michaelmangelsdorf/myth/myth.kicad_sch

## KiCad design myth.kicad_sch (2025-06-29)

Schematic: myth.kicad_sch

Parts:
J1, J2, J4, J5, J6: Conn_01x08_Male; PinHeader_1x08_P2.54mm_Vertical
R1: A7.5k; R_Axial_DIN0207_L6.3mm_D2.5mm_P10.16mm_Horizontal
RN1, RN2: R_Network08 100K; R_Array_SIP9
U1, U40, U105, U213: 74AHC02; DIP-14_W7.62mm_Socket_LongPads
U2, U21, U31, U60, U64, U81, U93, U124, U142, U173, U174, U176, U177, U178, U179: 74AHC04; DIP-14_W7.62mm_Socket_LongPads
U3, U50, U63, U127, U132: 74HC74; DIP-14_W7.62mm_Socket_LongPads
U4, U13, U24, U211: 74LS11
U5, U17, U79, U84, U88, U92, U121, U191: 74AHC273; DIP-20_W7.62mm_Socket_LongPads
U6, U28: 74LS21
U7, U12, U18, U42, U87, U95, U114, U152, U158, U159, U168, U169, U170, U171, U172, U190, U194, U200, U201, U203, U205, U206, U210, U214, U216: 74AHC08; DIP-14_W7.62mm_Socket_LongPads
U8, U14, U15, U23: 74LS154
U9, U102, U106, U143, U218, U220: 74LS08; DIP-14_W7.62mm_Socket_LongPads
U10: 74HC595; DIP-16_W7.62mm_Socket_LongPads
U11: 74HC165; DIP-16_W7.62mm_Socket_LongPads
U16, U128: 74LS27
U19: CD4532BE; DIP-16_W7.62mm_Socket_LongPads
U20, U22, U34, U35, U47, U141: 74AHC138; DIP-16_W7.62mm_Socket_LongPads
U25, U38, U65, U101, U123, U138, U140, U160, U161, U162, U163, U164, U165, U166, U167, U186, U187, U195, U196, U197, U199, U204, U208, U209, U215: 74LS32; DIP-14_W7.62mm_Socket_LongPads
U26: 74AHC374
U27, U51, U61, U62, U82, U89, U91, U96, U97, U99, U136: 74AHC244; DIP-20_W7.62mm_Socket_LongPads
U30: 4075
U32, U36, U90, U103, U129: 74HC00; DIP-14_W7.62mm_Socket_LongPads
U33: 74HC163; DIP-16_W7.62mm_Socket_LongPads
U39: 74HC238; DIP-16_W7.62mm_Socket_LongPads
U41, U59, U78: 74AHC574; DIP-20_W7.62mm_Socket_LongPads
U43, U44, U48, U49, U73, U74, U85, U86, U111, U112, U113, U122, U175, U180: 74HC157; DIP-16_W7.62mm_Socket_LongPads
U45, U46, U53, U54, U55, U56, U69, U70, U80, U83: 74HC193; DIP-16_W7.62mm_Socket_LongPads
U52: 74HC02; DIP-14_W7.62mm_Socket_LongPads
U57, U144, U145, U198, U212, U217, U219: 4075; DIP-14_W7.62mm_Socket_LongPads
U58, U75, U135: 4078
U66, U67: 74LS257; DIP-16_W7.62mm_Socket_LongPads
U71, U72, U94, U181: 74HC283; DIP-16_W7.62mm_Socket_LongPads
U76: KM62256CLP; DIP-28_W15.24mm
U77: SST39SF040; DIP-32_W15.24mm_Socket_LongPads
U98, U150, U151, U153, U154, U155, U156, U157, U207: 4070
U104, U107, U108, U116: 74LS08
U109, U110, U117, U119, U120, U125, U126, U130, U131, U147, U148, U149, U182, U183, U185, U188, U192, U193: 74LS573; DIP-16_W7.62mm_Socket_LongPads
U115: 4002
U133, U134, U137, U146, U202: 4072
U139, U189, U222: 74HC85
U184: 4068
X1: CxO_DIP14; Oscillator_DIP-14

Connections:
+5V: J4.1, R1.1, U3.2 (D), U5.20 (VCC), U8.19 (E1), U8.24 (VCC), U10.16 (VCC), U11.16 (VCC), U14.19 (E1), U14.24 (VCC), U15.18 (E0), U15.19 (E1), U15.24 (VCC), U17.20 (VCC), U19.16 (VDD), U20.6 (E3), U20.16 (VCC), U22.16 (VCC), U23.18 (E0), U23.19 (E1), U23.24 (VCC), U26.20 (VCC), U27.20 (VCC), U33.7 (CEP), U33.9 (~PE), U33.10 (CET), U33.16 (VCC), U34.16 (VCC), U35.16 (VCC), U39.6 (G1), U39.16 (VCC), U41.20 (VCC), U43.16 (VCC), U44.16 (VCC), U45.11 (~LOAD), U45.16 (VCC), U46.11 (~LOAD), U46.16 (VCC), U47.6 (E3), U47.16 (VCC), U48.16 (VCC), U49.16 (VCC), U50.2 (D), U50.12 (D), U51.20 (VCC), U53.5 (UP), U53.16 (VCC), U54.16 (VCC), U55.4 (DOWN), U55.16 (VCC), U56.4 (DOWN), U56.16 (VCC), U58.14 (Vdd), U59.20 (VCC), U62.8 (1A3), U62.11 (2A3), U62.13 (2A2), U62.15 (2A1), U62.17 (2A0), U62.20 (VCC), U63.2 (D), U66.16 (VCC), U67.16 (VCC), U69.16 (VCC), U70.16 (VCC), U71.16 (VCC), U72.16 (VCC), U73.16 (VCC), U74.16 (VCC), U75.14 (Vdd), U76.28 (VCC), U77.31 (PGM), U77.32 (VCC), U78.20 (VCC), U79.20 (VCC), U80.16 (VCC), U82.20 (VCC), U83.16 (VCC), U84.20 (VCC), U85.16 (VCC), U86.16 (VCC), U88.20 (VCC), U89.20 (VCC), U91.20 (VCC), U92.20 (VCC), U94.16 (VCC), U96.20 (VCC), U97.20 (VCC), U99.20 (VCC), U109.20 (VCC), U110.20 (VCC), U111.16 (VCC), U112.16 (VCC), U113.16 (VCC), U117.20 (VCC), U119.20 (VCC), U120.20 (VCC), U121.20 (VCC), U122.6 (I1b), U122.16 (VCC), U125.20 (VCC), U126.20 (VCC), U127.2 (D), U130.20 (VCC), U131.20 (VCC), U132.2 (D), U135.14 (Vdd), U136.2 (1A0), U136.4 (1A1), U136.6 (1A2), U136.8 (1A3), U136.11 (2A3), U136.13 (2A2), U136.15 (2A1), U136.20 (VCC), U139.3 (Ia=b), U139.16 (VCC), U141.6 (E3), U141.16 (VCC), U147.20 (VCC), U148.20 (VCC), U149.20 (VCC), U175.16 (VCC), U180.16 (VCC), U181.16 (VCC), U182.20 (VCC), U183.20 (VCC), U184.14 (Vdd), U185.20 (VCC), U188.20 (VCC), U189.16 (VCC), U191.20 (VCC), U192.20 (VCC), U193.20 (VCC), U222.3 (Ia=b), U222.16 (VCC), X1.1 (EN), X1.14 (Vcc)
A0: U80.3 (QA), U91.2 (1A0), U124.9, U135.12, U139.10 (A0), U153.1, U159.12, U164.12, U175.2 (I0a), U191.3 (D0), U193.3 (D1), U201.13
A1: U80.2 (QB), U91.4 (1A1), U135.11, U139.12 (A1), U142.9, U151.1, U160.12, U168.12, U175.5 (I0b), U185.2 (D0), U191.4 (D1), U193.4 (D2)
A2: U80.6 (QC), U91.6 (1A2), U135.10, U139.13 (A2), U150.2, U165.13, U170.13, U173.9, U175.11 (I0c), U185.3 (D1), U191.7 (D2), U193.5 (D3)
A3: U80.7 (QD), U91.8 (1A3), U98.2, U135.9, U139.15 (A3), U161.13, U169.13, U174.9, U175.14 (I0d), U185.4 (D2), U191.8 (D3), U193.6 (D4)
A4: U83.3 (QA), U91.17 (2A0), U135.5, U156.2, U163.12, U171.13, U177.9, U180.2 (I0a), U185.5 (D3), U189.10 (A0), U191.13 (D4), U193.7 (D5)
A5: U83.2 (QB), U91.15 (2A1), U135.4, U157.2, U167.12, U172.13, U178.9, U180.5 (I0b), U185.6 (D4), U189.12 (A1), U191.14 (D5), U193.8 (D6)
A6: U83.6 (QC), U91.13 (2A2), U135.3, U152.12, U154.1, U162.13, U176.9, U180.11 (I0c), U185.7 (D5), U189.13 (A2), U191.17 (D6), U193.9 (D7)
A7: U42.9, U83.7 (QD), U91.11 (2A3), U135.2, U155.1, U158.12, U166.13, U179.9, U180.14 (I0d), U185.8 (D6), U189.15 (A3), U191.18 (D7), U200.12, U203.12, U207.2
ADDC: U194.13, U208.13
ADDV: U213.3, U216.12
AEX: U212.12
AGX: U212.13
ALX: U212.11
ASR: U203.13, U204.12
B0: U69.3 (QA), U78.2 (D0), U89.2 (1A0), U109.2 (D0), U117.2 (D0), U120.2 (D0), U125.2 (D0), U130.2 (D0)
B1: U69.2 (QB), U78.3 (D1), U89.4 (1A1), U109.3 (D1), U117.3 (D1), U120.3 (D1), U125.3 (D1), U130.3 (D1)
B2: U69.6 (QC), U78.4 (D2), U89.6 (1A2), U109.4 (D2), U117.4 (D2), U120.4 (D2), U125.4 (D2), U130.4 (D2)
B3: U69.7 (QD), U78.5 (D3), U89.8 (1A3), U109.5 (D3), U117.5 (D3), U120.5 (D3), U125.5 (D3), U130.5 (D3)
B4: U70.3 (QA), U78.6 (D4), U89.17 (2A0), U109.6 (D4), U117.6 (D4), U120.6 (D4), U125.6 (D4), U130.6 (D4)
B5: U70.2 (QB), U78.7 (D5), U89.15 (2A1), U109.7 (D5), U117.7 (D5), U120.7 (D5), U125.7 (D5), U130.7 (D5)
B6: U70.6 (QC), U78.8 (D6), U89.13 (2A2), U109.8 (D6), U117.8 (D6), U120.8 (D6), U125.8 (D6), U130.8 (D6)
B7: U70.7 (QD), U78.9 (D7), U89.11 (2A3), U109.9 (D7), U117.9 (D7), U120.9 (D7), U125.9 (D7), U130.9 (D7)
BOIA: U47.7 (O7), U187.12
BOP1: U47.14 (O1), U120.11 (Load), U126.11 (Load)
BOP2: U47.12 (O3), U125.11 (Load), U131.11 (Load)
BOP3: U47.10 (O5), U117.11 (Load), U119.11 (Load)
BUSY: J6.6, U132.5 (Q)
C0: U86.3 (I1a), U92.2 (Q0), U96.2 (1A0)
C1: U86.6 (I1b), U92.5 (Q1), U96.4 (1A1)
C2: U86.10 (I1c), U92.6 (Q2), U96.6 (1A2)
C3: U86.13 (I1d), U92.9 (Q3), U96.8 (1A3)
C4: U85.3 (I1a), U92.12 (Q4), U96.17 (2A0)
C5: U85.6 (I1b), U92.15 (Q5), U96.15 (2A1)
C6: U85.10 (I1c), U92.16 (Q6), U96.13 (2A2)
C7: U85.13 (I1d), U92.19 (Q7), U96.11 (2A3)
CAN_OVERFLOW: U210.13
CARRY: U173.1, U181.9 (C4), U194.12
CLEAR_A: U202.1
CLOCK: J2.1, U33.2 (CP)
CLOSE: J6.8, U1.6, U7.12, U12.12, U33.11 (Q3), U39.4 (~G2A), U40.2, U40.6, U42.12, U59.11 (Cp), U78.11 (Cp), U84.11 (Cp), U188.11 (Load), U191.11 (Cp)
CNEW0: U75.2, U88.2 (Q0), U92.3 (D0)
CNEW1: U75.3, U88.5 (Q1), U92.4 (D1)
CNEW2: U75.4, U88.6 (Q2), U92.7 (D2)
CNEW3: U75.5, U88.9 (Q3), U92.8 (D3)
CNEW4: U75.9, U88.12 (Q4), U92.13 (D4)
CNEW5: U75.10, U88.15 (Q5), U92.14 (D5)
CNEW6: U75.11, U88.16 (Q6), U92.17 (D6)
CNEW7: U75.12, U88.19 (Q7), U92.18 (D7)
CODE: U16.13, U123.13, U141.14 (O1), U219.12
COR: U28.5, U30.2
D0: U53.3 (QA), U58.2, U59.2 (D0)
D1: U53.2 (QB), U58.3, U59.3 (D1)
D2: U53.6 (QC), U58.4, U59.4 (D2)
D3: U53.7 (QD), U58.5, U59.5 (D3)
D4: U54.3 (QA), U58.9, U59.6 (D4)
D5: U54.2 (QB), U58.10, U59.7 (D5)
D6: U54.6 (QC), U58.11, U59.8 (D6)
D7: U54.7 (QD), U58.12, U59.9 (D7)
DB0: RN2.2 (R1), U10.15 (QA), U11.11 (D0), U17.3 (D0), U26.2 (O0), U27.18 (1Y0), U41.2 (D0), U43.3 (I1a), U45.15 (A), U53.15 (A), U59.19 (Q0), U71.6 (B1), U73.2 (I0a), U76.11 (Q0), U77.13 (D0), U80.15 (A), U82.18 (1Y0), U86.2 (I0a), U88.3 (D0), U89.18 (1Y0), U91.18 (1Y0), U97.18 (1Y0), U110.19 (Q0), U111.2 (I0a), U119.19 (Q0), U126.19 (Q0), U131.19 (Q0), U136.18 (1Y0), U147.19 (Q0), U148.19 (Q0), U149.19 (Q0), U182.19 (Q0), U183.19 (Q0), U185.19 (Q0), U188.19 (Q0), U192.19 (Q0), U193.19 (Q0)
DB1: RN2.3 (R2), U10.1 (QB), U11.12 (D1), U17.4 (D1), U26.5 (O1), U27.16 (1Y1), U41.3 (D1), U43.6 (I1b), U45.1 (B), U53.1 (B), U59.18 (Q1), U71.2 (B2), U73.5 (I0b), U76.12 (Q1), U77.14 (D1), U80.1 (B), U82.16 (1Y1), U86.5 (I0b), U88.4 (D1), U89.16 (1Y1), U91.16 (1Y1), U97.16 (1Y1), U110.18 (Q1), U111.5 (I0b), U119.18 (Q1), U126.18 (Q1), U131.18 (Q1), U136.16 (1Y1), U147.18 (Q1), U148.18 (Q1), U149.18 (Q1), U182.18 (Q1), U183.18 (Q1), U185.18 (Q1), U188.18 (Q1), U192.18 (Q1), U193.18 (Q1)
DB2: RN2.4 (R3), U10.2 (QC), U11.13 (D2), U17.7 (D2), U26.6 (O2), U27.14 (1Y2), U41.4 (D2), U43.10 (I1c), U45.10 (C), U53.10 (C), U59.17 (Q2), U71.15 (B3), U73.11 (I0c), U76.13 (Q2), U77.15 (D2), U80.10 (C), U82.14 (1Y2), U86.11 (I0c), U88.7 (D2), U89.14 (1Y2), U91.14 (1Y2), U97.14 (1Y2), U110.17 (Q2), U111.11 (I0c), U119.17 (Q2), U126.17 (Q2), U131.17 (Q2), U136.14 (1Y2), U147.17 (Q2), U148.17 (Q2), U149.17 (Q2), U182.17 (Q2), U183.17 (Q2), U185.17 (Q2), U188.17 (Q2), U192.17 (Q2), U193.17 (Q2)
DB3: RN2.5 (R4), U10.3 (QD), U11.14 (D3), U17.8 (D3), U26.9 (O3), U27.12 (1Y3), U41.5 (D3), U43.13 (I1d), U45.9 (D), U53.9 (D), U59.16 (Q3), U71.11 (B4), U73.14 (I0d), U76.15 (Q3), U77.17 (D3), U80.9 (D), U82.12 (1Y3), U86.14 (I0d), U88.8 (D3), U89.12 (1Y3), U91.12 (1Y3), U97.12 (1Y3), U110.16 (Q3), U111.14 (I0d), U119.16 (Q3), U126.16 (Q3), U131.16 (Q3), U136.12 (1Y3), U147.16 (Q3), U148.16 (Q3), U149.16 (Q3), U182.16 (Q3), U183.16 (Q3), U185.16 (Q3), U188.16 (Q3), U192.16 (Q3), U193.16 (Q3)
DB4: RN2.6 (R5), U10.4 (QE), U11.3 (D4), U17.13 (D4), U26.12 (O4), U27.3 (2Y0), U41.6 (D4), U44.3 (I1a), U46.15 (A), U54.15 (A), U59.15 (Q4), U72.6 (B1), U74.2 (I0a), U76.16 (Q4), U77.18 (D4), U82.3 (2Y0), U83.15 (A), U85.2 (I0a), U88.13 (D4), U89.3 (2Y0), U91.3 (2Y0), U97.3 (2Y0), U110.15 (Q4), U119.15 (Q4), U122.2 (I0a), U126.15 (Q4), U131.15 (Q4), U136.3 (2Y0), U147.15 (Q4), U148.15 (Q4), U149.15 (Q4), U182.15 (Q4), U183.15 (Q4), U185.15 (Q4), U188.15 (Q4), U192.15 (Q4), U193.15 (Q4)
DB5: RN2.7 (R6), U10.5 (QF), U11.4 (D5), U17.14 (D5), U26.15 (O5), U27.5 (2Y1), U41.7 (D5), U44.6 (I1b), U46.1 (B), U54.1 (B), U59.14 (Q5), U72.2 (B2), U74.5 (I0b), U76.17 (Q5), U77.19 (D5), U82.5 (2Y1), U83.1 (B), U85.5 (I0b), U88.14 (D5), U89.5 (2Y1), U91.5 (2Y1), U97.5 (2Y1), U110.14 (Q5), U119.14 (Q5), U122.5 (I0b), U126.14 (Q5), U131.14 (Q5), U136.5 (2Y1), U147.14 (Q5), U148.14 (Q5), U149.14 (Q5), U182.14 (Q5), U183.14 (Q5), U185.14 (Q5), U188.14 (Q5), U192.14 (Q5), U193.14 (Q5)
DB6: RN2.8 (R7), U10.6 (QG), U11.5 (D6), U17.17 (D6), U26.16 (O6), U27.7 (2Y2), U41.8 (D6), U44.10 (I1c), U46.10 (C), U54.10 (C), U59.13 (Q6), U72.15 (B3), U74.11 (I0c), U76.18 (Q6), U77.20 (D6), U82.7 (2Y2), U83.10 (C), U85.11 (I0c), U88.17 (D6), U89.7 (2Y2), U91.7 (2Y2), U97.7 (2Y2), U110.13 (Q6), U119.13 (Q6), U122.11 (I0c), U126.13 (Q6), U131.13 (Q6), U136.7 (2Y2), U147.13 (Q6), U148.13 (Q6), U149.13 (Q6), U182.13 (Q6), U183.13 (Q6), U185.13 (Q6), U188.13 (Q6), U192.13 (Q6), U193.13 (Q6)
DB7: RN2.9 (R8), U9.5, U10.7 (QH), U11.6 (D7), U17.18 (D7), U26.19 (O7), U27.9 (2Y3), U41.9 (D7), U44.13 (I1d), U46.9 (D), U54.9 (D), U59.12 (Q7), U72.11 (B4), U74.14 (I0d), U76.19 (Q7), U77.21 (D7), U82.9 (2Y3), U83.9 (D), U85.14 (I0d), U88.18 (D7), U89.9 (2Y3), U91.9 (2Y3), U93.1, U97.9 (2Y3), U110.12 (Q7), U119.12 (Q7), U122.14 (I0d), U126.12 (Q7), U131.12 (Q7), U136.9 (2Y3), U147.12 (Q7), U148.12 (Q7), U149.12 (Q7), U182.12 (Q7), U183.12 (Q7), U185.12 (Q7), U188.12 (Q7), U192.12 (Q7), U193.12 (Q7)
DEC: U141.9 (O6)
DID_OVERFLOW: U210.11, U216.13
DPH: U33.12 (Q2), U35.6 (E3), U39.3 (A2), U40.5
EA: U141.7 (O7)
EH0: U15.23 (A0), U17.12 (Q4), U97.17 (2A0)
EH1: U15.22 (A1), U17.15 (Q5), U97.15 (2A1)
EH2: U15.21 (A2), U17.16 (Q6), U97.13 (2A2)
EH3: U15.20 (A3), U17.19 (Q7), U97.11 (2A3)
EL0: U17.2 (Q0), U23.23 (A0), U97.2 (1A0)
EL1: U17.5 (Q1), U23.22 (A1), U97.4 (1A1)
EL2: U17.6 (Q2), U23.21 (A2), U97.6 (1A2)
EL3: U17.9 (Q3), U23.20 (A3), U97.8 (1A3)
ENTER: U141.11 (O4)
EXIT: U48.1 (S), U49.1 (S), U85.1 (S), U86.1 (S), U88.11 (Cp), U115.3, U123.12
FBIT0: U196.12, U199.11
FBIT7: U197.13, U201.11
FEQ: U189.6 (Oa=b), U198.13
FETCH: U66.1 (S), U67.1 (S)
FGT: U189.5 (Oa>b), U198.11
FLT: U189.7 (Oa<b), U198.12
Fx: U38.13
GET: U128.2
GETB: U115.4
GETD: U105.3
GETO: U57.12
GETPUT: U1.1, U32.1, U32.10, U34.6 (E3), U60.11, U61.1 (1OE), U61.19 (2OE)
GND: J6.5, RN1.1 (common), RN2.1 (common), U3.3 (C), U5.10 (GND), U8.12 (GND), U10.8 (GND), U11.8 (GND), U11.10 (DS), U11.15 (~CE), U14.12 (GND), U15.12 (GND), U17.10 (GND), U19.2 (D5), U19.3 (D6), U19.4 (D7), U19.8 (VSS), U20.5 (E2), U20.8 (GND), U22.4 (E1), U22.8 (GND), U23.12 (GND), U26.10 (GND), U27.10 (GND), U27.11 (2A3), U27.13 (2A2), U27.15 (2A1), U33.3 (D0), U33.4 (D1), U33.5 (D2), U33.6 (D3), U33.8 (GND), U34.4 (E1), U34.5 (E2), U34.8 (GND), U35.8 (GND), U39.5 (~G2B), U39.8 (GND), U41.10 (GND), U43.8 (GND), U43.15 (E), U44.8 (GND), U44.15 (E), U45.8 (GND), U46.8 (GND), U47.5 (E2), U47.8 (GND), U48.8 (GND), U48.15 (E), U49.8 (GND), U49.15 (E), U50.3 (C), U50.11 (C), U51.10 (GND), U53.8 (GND), U54.8 (GND), U55.8 (GND), U56.8 (GND), U58.7 (Vss), U59.10 (GND), U61.10 (GND), U62.10 (GND), U63.3 (C), U66.8 (GND), U66.15 (OE), U67.8 (GND), U67.15 (OE), U69.8 (GND), U70.8 (GND), U71.7 (C0), U71.8 (GND), U72.8 (GND), U73.8 (GND), U73.15 (E), U74.8 (GND), U74.15 (E), U75.7 (Vss), U76.14 (GND), U77.1 (A18), U77.2 (A16), U77.3 (A15), U77.16 (GND), U77.30 (A17), U78.10 (GND), U79.10 (GND), U80.8 (GND), U82.10 (GND), U83.8 (GND), U84.10 (GND), U85.8 (GND), U85.15 (E), U86.8 (GND), U86.15 (E), U88.10 (GND), U89.10 (GND), U91.10 (GND), U92.10 (GND), U94.8 (GND), U96.10 (GND), U97.10 (GND), U99.10 (GND), U109.10 (GND), U110.10 (GND), U111.3 (I1a), U111.6 (I1b), U111.8 (GND), U111.10 (I1c), U111.13 (I1d), U111.15 (E), U112.8 (GND), U112.15 (E), U113.8 (GND), U113.15 (E), U117.10 (GND), U119.10 (GND), U120.10 (GND), U121.10 (GND), U122.3 (I1a), U122.8 (GND), U122.10 (I1c), U122.13 (I1d), U122.15 (E), U125.10 (GND), U126.10 (GND), U127.3 (C), U130.10 (GND), U131.10 (GND), U132.3 (C), U135.7 (Vss), U136.10 (GND), U136.17 (2A0), U139.2 (Ia<b), U139.4 (Ia>b), U139.8 (GND), U141.4 (E1), U141.8 (GND), U147.10 (GND), U148.10 (GND), U149.10 (GND), U175.8 (GND), U175.15 (E), U180.8 (GND), U180.15 (E), U181.8 (GND), U182.10 (GND), U183.10 (GND), U184.7 (Vss), U185.10 (GND), U188.10 (GND), U189.8 (GND), U191.10 (GND), U192.10 (GND), U193.2 (D0), U193.10 (GND), U222.2 (Ia<b), U222.4 (Ia>b), U222.8 (GND), U222.15 (A3), X1.7 (GND)
HI0: U51.18 (1Y0), U76.25 (A8), U77.27 (A8), U78.19 (Q0), U96.18 (1Y0), U99.18 (1Y0), U112.3 (I1a), U130.19 (Q0)
HI1: U51.16 (1Y1), U76.24 (A9), U77.26 (A9), U78.18 (Q1), U96.16 (1Y1), U99.16 (1Y1), U112.6 (I1b), U130.18 (Q1)
HI2: U51.14 (1Y2), U76.21 (A10), U77.23 (A10), U78.17 (Q2), U96.14 (1Y2), U99.14 (1Y2), U112.10 (I1c), U130.17 (Q2)
HI3: U51.12 (1Y3), U76.23 (A11), U77.25 (A11), U78.16 (Q3), U96.12 (1Y3), U99.12 (1Y3), U112.13 (I1d), U130.16 (Q3)
HI4: U51.3 (2Y0), U76.2 (A12), U77.4 (A12), U78.15 (Q4), U96.3 (2Y0), U99.3 (2Y0), U113.3 (I1a), U130.15 (Q4)
HI5: U51.5 (2Y1), U76.26 (A13), U77.28 (A13), U78.14 (Q5), U96.5 (2Y1), U99.5 (2Y1), U113.6 (I1b), U130.14 (Q5)
HI6: U51.7 (2Y2), U76.1 (A14), U77.29 (A14), U78.13 (Q6), U96.7 (2Y2), U99.7 (2Y2), U113.10 (I1c), U130.13 (Q6)
HI7: U51.9 (2Y3), U64.1, U77.22 (CE), U78.12 (Q7), U96.9 (2Y3), U99.9 (2Y3), U113.13 (I1d), U130.12 (Q7)
IABO: U47.9 (O6), U138.12
IA_LE: U109.11 (Load), U110.11 (Load), U187.11
IB0: RN1.2 (R1), RN1.9 (R8), U5.2 (Q0), U5.19 (Q7), U8.23 (A0), U14.23 (A0), U19.1 (D4), U20.1 (A0), U26.3 (D0), U26.18 (D7), U27.2 (1A0), U41.12 (Q7), U41.19 (Q0), U47.1 (A0), U62.2 (1A0), U141.1 (A0), U142.1, U222.9 (B0)
IB0_pre: U5.3 (D0), U111.4 (Za)
IB1: RN1.3 (R2), RN1.8 (R7), U5.5 (Q1), U5.16 (Q6), U8.22 (A1), U14.22 (A1), U19.13 (D3), U20.2 (A1), U26.4 (D1), U26.17 (D6), U27.4 (1A1), U35.3 (A2), U41.13 (Q6), U41.18 (Q1), U47.2 (A1), U62.4 (1A1), U141.2 (A1), U145.11, U146.4, U222.11 (B1), U222.13 (A2)
IB1_pre: U5.4 (D1), U111.7 (Zb)
IB2: RN1.4 (R3), RN1.7 (R6), U5.6 (Q2), U5.15 (Q5), U8.21 (A2), U14.21 (A2), U19.12 (D2), U20.3 (A2), U26.7 (D2), U26.14 (D5), U27.6 (1A2), U34.2 (A1), U35.2 (A1), U41.14 (Q5), U41.17 (Q2), U47.3 (A2), U62.6 (1A2), U141.3 (A2), U145.12, U146.3, U222.12 (A1), U222.14 (B2)
IB2_pre: U5.7 (D2), U111.9 (Zc)
IB3: RN1.5 (R4), RN1.6 (R5), U5.9 (Q3), U5.12 (Q4), U8.20 (A3), U14.20 (A3), U19.10 (D0), U19.11 (D1), U26.8 (D3), U26.13 (D4), U27.8 (1A3), U27.17 (2A0), U31.1, U32.9, U34.1 (A0), U34.3 (A2), U35.1 (A0), U41.15 (Q4), U41.16 (Q3), U145.13, U146.2, U222.1 (B3), U222.10 (A0)
IB3_pre: U5.8 (D3), U111.12 (Zd)
IB4_pre: U5.13 (D4), U122.4 (Za)
IB5_pre: U5.14 (D5), U122.7 (Zb)
IB6_pre: U5.17 (D6), U122.9 (Zc)
IB7_pre: U5.18 (D7), U122.12 (Zd)
INC: U141.10 (O5)
IPH: U16.2, U40.4, U128.1
JUMP: U36.4, U43.1 (S), U44.1 (S), U137.1
KEY: U65.5, U130.11 (Load), U217.10
L0: U45.3 (QA), U51.2 (1A0), U99.2 (1A0)
L1: U45.2 (QB), U51.4 (1A1), U99.4 (1A1)
L2: U45.6 (QC), U51.6 (1A2), U99.6 (1A2)
L3: U45.7 (QD), U51.8 (1A3), U99.8 (1A3)
L4: U46.3 (QA), U51.17 (2A0), U99.17 (2A0)
L5: U46.2 (QB), U51.15 (2A1), U99.15 (2A1)
L6: U46.6 (QC), U51.13 (2A2), U99.13 (2A2)
L7: U46.7 (QD), U51.11 (2A3), U99.11 (2A3)
LATCH_POINTER: U133.1, U134.2, U219.11
LEAVE: U141.12 (O3)
LFETCH: U16.1, U40.3, U143.11
LL0: U61.18 (1Y0), U62.18 (1Y0), U66.2 (I0a)
LL1: U61.16 (1Y1), U62.16 (1Y1), U66.5 (I0b)
LL2: U61.14 (1Y2), U62.14 (1Y2), U66.14 (I0c)
LL3: U61.12 (1Y3), U62.12 (1Y3), U66.11 (I0d)
LL4: U61.3 (2Y0), U62.3 (2Y0), U67.2 (I0a)
LL5: U61.5 (2Y1), U62.5 (2Y1), U67.5 (I0b)
LL6: U61.7 (2Y2), U62.7 (2Y2), U67.14 (I0c)
LL7: U61.9 (2Y3), U62.9 (2Y3), U67.11 (I0d)
LO0: U66.4 (Za), U76.10 (A0), U77.12 (A0)
LO1: U66.7 (Zb), U76.9 (A1), U77.11 (A1)
LO2: U66.12 (Zc), U76.8 (A2), U77.10 (A2)
LO3: U66.9 (Zd), U76.7 (A3), U77.9 (A3)
LO4: U67.4 (Za), U76.6 (A4), U77.8 (A4)
LO5: U67.7 (Zb), U76.5 (A5), U77.7 (A5)
LO6: U67.12 (Zc), U76.4 (A6), U77.6 (A6)
LO7: U67.9 (Zd), U76.3 (A7), U77.5 (A7)
LOCAL: U138.13, U141.13 (O2)
MISO: J6.3, R1.2, U2.11
MOSI: J6.2, U11.9 (Q7)
Mx: U38.12
Mx_pre: U52.5
NOTA0: U124.8, U175.3 (I1a), U192.2 (D0)
NOTA1: U142.8, U175.6 (I1b), U192.3 (D1)
NOTA2: U173.8, U175.10 (I1c), U192.4 (D2)
NOTA3: U174.8, U175.13 (I1d), U192.5 (D3)
NOTA4: U177.8, U180.3 (I1a), U192.6 (D4)
NOTA5: U178.8, U180.6 (I1b), U192.7 (D5)
NOTA6: U176.8, U180.10 (I1c), U192.8 (D6)
NOTA7: U179.8, U180.13 (I1d), U192.9 (D7)
NZFLAG_A: U7.4, U135.1
NZFLAG_D: U7.9, U58.1
unnamed: U1.4, U33.1 (~MR)
unnamed: U1.13, U3.1 (~R)
unnamed: U2.10, U2.13
unnamed: U4.2, U63.5 (Q)
unnamed: U9.6, U90.4
unnamed: U2.12, U10.14 (SER)
unnamed: U12.8, U38.4
unnamed: U12.11, U92.11 (Cp)
unnamed: U12.13, U50.5 (Q)
unnamed: U6.5, U13.12
unnamed: U14.18 (E0), U174.2
unnamed: U16.12, U96.1 (1OE), U96.19 (2OE)
unnamed: U19.6 (Q2), U22.3 (A2)
unnamed: U19.7 (Q1), U22.2 (A1)
unnamed: U19.9 (Q0), U22.1 (A0)
unnamed: U19.14 (GS), U22.6 (E3)
unnamed: U28.1, U36.6
unnamed: U30.9, U32.4
unnamed: U31.2, U32.2
unnamed: U33.13 (Q1), U39.2 (A1)
unnamed: U33.14 (Q0), U39.1 (A0)
unnamed: U38.5, U42.8
unnamed: U40.1, U55.5 (UP)
unnamed: U42.11, U53.4 (DOWN)
unnamed: U48.2 (I0a), U73.4 (Za)
unnamed: U48.4 (Za), U79.3 (D0)
unnamed: U48.5 (I0b), U73.7 (Zb)
unnamed: U48.7 (Zb), U79.4 (D1)
unnamed: U48.9 (Zc), U79.7 (D2)
unnamed: U48.11 (I0c), U73.9 (Zc)
unnamed: U48.12 (Zd), U79.8 (D3)
unnamed: U48.14 (I0d), U73.12 (Zd)
unnamed: U49.2 (I0a), U74.4 (Za)
unnamed: U49.4 (Za), U79.13 (D4)
unnamed: U49.5 (I0b), U74.7 (Zb)
unnamed: U49.7 (Zb), U79.14 (D5)
unnamed: U49.9 (Zc), U79.17 (D6)
unnamed: U49.11 (I0c), U74.9 (Zc)
unnamed: U49.12 (Zd), U79.18 (D7)
unnamed: U49.14 (I0d), U74.12 (Zd)
unnamed: U7.13, U50.9 (Q)
unnamed: U51.1 (1OE), U51.19 (2OE), U60.10, U62.1 (1OE), U62.19 (2OE)
unnamed: U52.4, U65.12
unnamed: U55.12 (~CO), U56.5 (UP)
unnamed: U55.14 (CLR), U56.14 (CLR), U65.3
unnamed: U7.11, U65.1
unnamed: U65.11, U78.1 (OE)
unnamed: U71.1 (S2), U73.6 (I1b)
unnamed: U71.4 (S1), U73.3 (I1a)
unnamed: U71.9 (C4), U72.7 (C0)
unnamed: U71.10 (S4), U73.13 (I1d)
unnamed: U71.13 (S3), U73.10 (I1c)
unnamed: U72.1 (S2), U74.6 (I1b)
unnamed: U72.4 (S1), U74.3 (I1a)
unnamed: U72.10 (S4), U74.13 (I1d)
unnamed: U72.13 (S3), U74.10 (I1c)
unnamed: U9.4, U81.2
unnamed: U91.1 (1OE), U91.19 (2OE), U95.11
unnamed: U101.11, U129.5
unnamed: U101.13, U102.11
unnamed: U72.9 (C4), U81.1, U102.4
unnamed: U93.2, U102.5
unnamed: U102.6, U103.4
unnamed: U104.11, U128.13
unnamed: U38.11, U104.13
unnamed: U53.11 (~LOAD), U54.11 (~LOAD), U105.1
unnamed: U45.4 (DOWN), U107.11
unnamed: U45.5 (UP), U108.11
unnamed: U4.12, U111.1 (S), U122.1 (S)
unnamed: U112.1 (S), U113.1 (S), U115.5, U219.10
unnamed: U86.4 (Za), U112.2 (I0a)
unnamed: U69.15 (A), U112.4 (Za)
unnamed: U86.7 (Zb), U112.5 (I0b)
unnamed: U69.1 (B), U112.7 (Zb)
unnamed: U69.10 (C), U112.9 (Zc)
unnamed: U86.9 (Zc), U112.11 (I0c)
unnamed: U69.9 (D), U112.12 (Zd)
unnamed: U86.12 (Zd), U112.14 (I0d)
unnamed: U85.4 (Za), U113.2 (I0a)
unnamed: U70.15 (A), U113.4 (Za)
unnamed: U85.7 (Zb), U113.5 (I0b)
unnamed: U70.1 (B), U113.7 (Zb)
unnamed: U70.10 (C), U113.9 (Zc)
unnamed: U85.9 (Zc), U113.11 (I0c)
unnamed: U70.9 (D), U113.12 (Zd)
unnamed: U85.12 (Zd), U113.14 (I0d)
unnamed: U59.1 (OE), U114.11
unnamed: U69.11 (~LOAD), U70.11 (~LOAD), U115.1
unnamed: U121.3 (D0), U196.11
unnamed: U121.4 (D1), U191.5 (Q1)
unnamed: U121.7 (D2), U191.6 (Q2)
unnamed: U121.8 (D3), U191.9 (Q3)
unnamed: U121.11 (Cp), U190.11
unnamed: U121.13 (D4), U191.12 (Q4)
unnamed: U121.14 (D5), U191.15 (Q5)
unnamed: U121.17 (D6), U191.16 (Q6)
unnamed: U121.18 (D7), U197.11
unnamed: U63.4 (~S), U123.3
unnamed: U57.11, U123.11
unnamed: U80.11 (~LOAD), U83.11 (~LOAD), U124.1, U209.11
unnamed: U124.2, U190.12
unnamed: U42.13, U127.5 (Q)
unnamed: U76.27 (~WE), U129.6
unnamed: U4.13, U132.6 (~Q)
unnamed: U133.5, U138.11
unnamed: U79.11 (Cp), U134.1
unnamed: U57.10, U134.5
unnamed: U7.8, U137.2
unnamed: U7.6, U137.4
unnamed: U38.6, U137.5
unnamed: U139.5 (Oa>b), U189.4 (Ia>b)
unnamed: U139.6 (Oa=b), U189.3 (Ia=b)
unnamed: U139.7 (Oa<b), U189.2 (Ia<b)
unnamed: U89.1 (1OE), U89.19 (2OE), U140.11
unnamed: U24.12, U140.13
unnamed: U141.15 (O0), U218.12
unnamed: U142.2, U146.5
unnamed: U147.2 (D0), U164.11
unnamed: U147.3 (D1), U160.11
unnamed: U147.4 (D2), U165.11
unnamed: U147.5 (D3), U161.11
unnamed: U147.6 (D4), U163.11
unnamed: U147.7 (D5), U167.11
unnamed: U147.8 (D6), U162.11
unnamed: U147.9 (D7), U166.11
unnamed: U148.2 (D0), U159.11
unnamed: U148.3 (D1), U168.11
unnamed: U148.4 (D2), U170.11
unnamed: U148.5 (D3), U169.11
unnamed: U148.6 (D4), U171.11
unnamed: U148.7 (D5), U172.11
unnamed: U148.8 (D6), U152.11
unnamed: U148.9 (D7), U158.11
unnamed: U149.2 (D0), U153.3
unnamed: U149.3 (D1), U151.3
unnamed: U149.4 (D2), U150.3
unnamed: U98.3, U149.5 (D3)
unnamed: U149.6 (D4), U156.3
unnamed: U149.7 (D5), U157.3
unnamed: U149.8 (D6), U154.3
unnamed: U173.2, U206.12
unnamed: U94.5 (A1), U175.4 (Za)
unnamed: U94.3 (A2), U175.7 (Zb)
unnamed: U94.14 (A3), U175.9 (Zc)
unnamed: U94.12 (A4), U175.12 (Zd)
unnamed: U180.4 (Za), U181.5 (A1)
unnamed: U180.7 (Zb), U181.3 (A2)
unnamed: U180.9 (Zc), U181.14 (A3)
unnamed: U180.12 (Zd), U181.12 (A4)
unnamed: U181.1 (S2), U182.7 (D5)
unnamed: U181.4 (S1), U182.6 (D4)
unnamed: U94.9 (C4), U181.7 (C0)
unnamed: U181.13 (S3), U182.8 (D6)
unnamed: U182.1 (OE), U211.12
unnamed: U94.4 (S1), U182.2 (D0)
unnamed: U94.1 (S2), U182.3 (D1)
unnamed: U94.13 (S3), U182.4 (D2)
unnamed: U94.10 (S4), U182.5 (D3)
unnamed: U183.1 (OE), U213.1
unnamed: U183.2 (D0), U183.3 (D1), U183.4 (D2), U183.5 (D3), U183.6 (D4), U183.7 (D5), U183.8 (D6), U183.9 (D7), U215.11
unnamed: U184.1 (K), U190.13
unnamed: U185.1 (OE), U205.11
unnamed: U185.9 (D7), U203.11
unnamed: U55.11 (~LOAD), U56.11 (~LOAD), U186.11
unnamed: U28.6, U186.12
unnamed: U87.11, U188.1 (OE)
unnamed: U191.2 (Q0), U196.13
unnamed: U191.19 (Q7), U197.12
unnamed: U194.11, U195.12
unnamed: U195.11, U199.12
unnamed: U195.13, U206.11
unnamed: U198.10, U214.12
unnamed: U199.13, U200.11
unnamed: U201.12, U202.5, U204.11
unnamed: U202.4, U208.11
unnamed: U207.3, U210.12
unnamed: U6.6, U209.12
unnamed: U212.10, U213.2, U214.13
unnamed: U214.11, U215.12
unnamed: U215.13, U216.11
unnamed: U65.6, U218.13
unnamed: U82.1 (1OE), U82.19 (2OE), U220.6
unnamed: U65.4, U222.6 (Oa=b)
O0: U79.2 (Q0), U82.2 (1A0), U84.3 (D0), U110.2 (D0), U119.2 (D0), U126.2 (D0), U131.2 (D0)
O1: U79.5 (Q1), U82.4 (1A1), U84.4 (D1), U110.3 (D1), U119.3 (D1), U126.3 (D1), U131.3 (D1)
O2: U79.6 (Q2), U82.6 (1A2), U84.7 (D2), U110.4 (D2), U119.4 (D2), U126.4 (D2), U131.4 (D2)
O3: U79.9 (Q3), U82.8 (1A3), U84.8 (D3), U110.5 (D3), U119.5 (D3), U126.5 (D3), U131.5 (D3)
O4: U79.12 (Q4), U82.17 (2A0), U84.13 (D4), U110.6 (D4), U119.6 (D4), U126.6 (D4), U131.6 (D4)
O5: U79.15 (Q5), U82.15 (2A1), U84.14 (D5), U110.7 (D5), U119.7 (D5), U126.7 (D5), U131.7 (D5)
O6: U79.16 (Q6), U82.13 (2A2), U84.17 (D6), U110.8 (D6), U119.8 (D6), U126.8 (D6), U131.8 (D6)
O7: U79.19 (Q7), U82.11 (2A3), U84.18 (D7), U110.9 (D7), U119.9 (D7), U126.9 (D7), U131.9 (D7)
O_PC_0: U43.2 (I0a), U61.2 (1A0), U71.5 (A1), U84.2 (Q0), U109.19 (Q0), U117.19 (Q0), U120.19 (Q0), U125.19 (Q0)
O_PC_1: U43.5 (I0b), U61.4 (1A1), U71.3 (A2), U84.5 (Q1), U109.18 (Q1), U117.18 (Q1), U120.18 (Q1), U125.18 (Q1)
O_PC_2: U43.11 (I0c), U61.6 (1A2), U71.14 (A3), U84.6 (Q2), U109.17 (Q2), U117.17 (Q2), U120.17 (Q2), U125.17 (Q2)
O_PC_3: U43.14 (I0d), U61.8 (1A3), U71.12 (A4), U84.9 (Q3), U109.16 (Q3), U117.16 (Q3), U120.16 (Q3), U125.16 (Q3)
O_PC_4: U44.2 (I0a), U61.17 (2A0), U72.5 (A1), U84.12 (Q4), U109.15 (Q4), U117.15 (Q4), U120.15 (Q4), U125.15 (Q4)
O_PC_5: U44.5 (I0b), U61.15 (2A1), U72.3 (A2), U84.15 (Q5), U109.14 (Q5), U117.14 (Q5), U120.14 (Q5), U125.14 (Q5)
O_PC_6: U44.11 (I0c), U61.13 (2A2), U72.14 (A3), U84.16 (Q6), U109.13 (Q6), U117.13 (Q6), U120.13 (Q6), U125.13 (Q6)
O_PC_7: U44.14 (I0d), U61.11 (2A3), U72.12 (A4), U84.19 (Q7), U109.12 (Q7), U117.12 (Q7), U120.12 (Q7), U125.12 (Q7)
P1BO: U47.15 (O0), U133.2
P2BO: U47.13 (O2), U133.3
P3BO: U47.11 (O4), U133.4
PAGE_0: U18.12, U75.13
PC0: U48.3 (I1a), U55.3 (QA), U66.3 (I1a)
PC1: U48.6 (I1b), U55.2 (QB), U66.6 (I1b)
PC2: U48.10 (I1c), U55.6 (QC), U66.13 (I1c)
PC3: U48.13 (I1d), U55.7 (QD), U66.10 (I1d)
PC4: U49.3 (I1a), U56.3 (QA), U67.3 (I1a)
PC5: U49.6 (I1b), U56.2 (QB), U67.6 (I1b)
PC6: U49.10 (I1c), U56.6 (QC), U67.13 (I1c)
PC7: U49.13 (I1d), U56.7 (QD), U67.10 (I1d)
PC_IN0: U43.4 (Za), U55.15 (A)
PC_IN1: U43.7 (Zb), U55.1 (B)
PC_IN2: U43.9 (Zc), U55.10 (C)
PC_IN3: U43.12 (Zd), U55.9 (D)
PC_IN4: U44.4 (Za), U56.15 (A)
PC_IN5: U44.7 (Zb), U56.1 (B)
PC_IN6: U44.9 (Zc), U56.10 (C)
PC_IN7: U44.12 (Zd), U56.9 (D)
PH0: U22.5 (E2), U39.15 (Y0)
PH1: U5.11 (Cp), U39.13 (Y2)
PH2: U39.11 (Y4)
PH3: U32.5, U36.5, U39.9 (Y6)
PHA3: U129.4, U143.12
PLE: J4.2, U15.2 (S1), U26.11 (Cp)
POE: J1.8, U23.2 (S1)
PUT: U101.12
PageNZ: U4.1, U75.1
RES: U1.5, U1.12, U45.14 (CLR), U46.14 (CLR), U53.14 (CLR), U54.14 (CLR), U65.2, U69.14 (CLR), U70.14 (CLR), U80.14 (CLR), U83.14 (CLR), U202.2
RET: U28.2, U30.8
SCL: U1.11
SCLK: J6.4, U3.5 (Q)
SCROUNGE: U35.5 (E2), U65.13, U144.11, U218.11
SH2: J4.3, U15.3 (S2)
SH3: J4.4, U15.4 (S3)
SH4: J4.5, U15.5 (S4)
SH5: J4.6, U15.6 (S5)
SH6: J4.7, U15.7 (S6)
SH7: J4.8, U15.8 (S7)
SH8: J5.1, U15.9 (S8)
SH9: J5.2, U15.10 (S9)
SH10: J5.3, U15.11 (S10)
SH11: J5.4, U15.13 (S11)
SH12: J5.5, U15.14 (S12)
SH13: J5.6, U15.15 (S13)
SH14: J5.7, U15.16 (S14)
SH15: J5.8, U15.17 (S15)
SHL: U200.13, U202.3
SHR: U204.13
SL2: J1.7, U23.3 (S2)
SL3: J1.6, U23.4 (S3)
SL4: J1.5, U23.5 (S4)
SL5: J1.4, U23.6 (S5)
SL6: J1.3, U23.7 (S6)
SL7: J1.2, U23.8 (S7)
SL8: J1.1, U23.9 (S8)
SL9: J2.8, U23.10 (S9)
SL10: J2.7, U23.11 (S10)
SL11: J2.6, U23.13 (S11)
SL12: J2.5, U23.14 (S12)
SL13: J2.4, U23.15 (S13)
SL14: J2.3, U23.16 (S14)
SL15: J2.2, U23.17 (S15)
SSI: U10.11 (SRCLK), U10.12 (RCLK)
SSO: U11.2 (CP)
SUBB: U94.7 (C0), U175.1 (S), U180.1 (S), U206.13, U208.12
SUBR: U21.9, U30.1, U38.3
SUM_BIT7: U181.10 (S4), U182.9 (D7), U207.1
TRAP: U18.13, U38.2, U140.12, U186.13, U187.13
TRAP_0: U18.11
X0: U94.6 (B1), U121.2 (Q0), U139.9 (B0), U153.2, U159.13, U164.13, U188.2 (D0)
X1: U94.2 (B2), U121.5 (Q1), U139.11 (B1), U151.2, U160.13, U168.13, U188.3 (D1)
X2: U94.15 (B3), U121.6 (Q2), U139.14 (B2), U150.1, U165.12, U170.12, U188.4 (D2)
X3: U94.11 (B4), U98.1, U121.9 (Q3), U139.1 (B3), U161.12, U169.12, U188.5 (D3)
X4: U121.12 (Q4), U156.1, U163.13, U171.12, U181.6 (B1), U188.6 (D4), U189.9 (B0)
X5: U121.15 (Q5), U157.1, U167.13, U172.12, U181.2 (B2), U188.7 (D5), U189.11 (B1)
X6: U121.16 (Q6), U152.13, U154.2, U162.12, U181.15 (B3), U188.8 (D6), U189.14 (B2)
X7: U121.19 (Q7), U155.2, U158.13, U166.12, U181.11 (B4), U188.9 (D7), U189.1 (B3)
ZFLAG_A: U12.9, U135.13
opc_ALU: U147.11 (Load), U148.11 (Load), U149.11 (Load), U182.11 (Load), U183.11 (Load), U185.11 (Load), U192.11 (Load), U193.11 (Load)
xB: U115.2
xC: U28.4, U38.1
xD: U14.6 (S5), U105.2
xE: U17.11 (Cp)
xH: U7.5
xJ: U137.3
xK: U134.4, U219.13
xM: U102.13
xM_pre: U52.6
xN: U42.10
xO: U57.13
xP: U41.11 (Cp)
xU: U73.1 (S), U74.1 (S), U90.5, U103.5, U134.3
xW_pre: U7.10
xZ: U12.10
~ADDC: U8.15 (S13), U211.2
~ADDV: U8.16 (S14), U211.1
~AEX: U8.3 (S2), U184.4 (C)
~AGX: U8.4 (S3), U184.5 (D)
~ALX: U8.2 (S1), U184.3 (B)
~AND: U8.5 (S4), U148.1 (OE), U184.9 (E)
~ASR: U8.14 (S12), U205.12
~Ax: U8.9 (S8), U13.13, U35.11 (O4), U95.13
~BOA: U80.13 (~BO), U83.4 (DOWN)
~BOB: U69.13 (~BO), U70.4 (DOWN)
~BOD: U53.13 (~BO), U54.4 (DOWN)
~BOL: U45.13 (~BO), U46.4 (DOWN)
~Bx: U24.13, U35.13 (O2)
~CAN_OVERFLOW: U149.9 (D7), U155.3
~CLEAR_A: U191.1 (~Mr)
~CLOSE: U63.1 (~R)
~COA: U80.12 (~CO), U83.5 (UP)
~COB: U69.12 (~CO), U70.5 (UP)
~COD: U53.12 (~CO), U54.5 (UP)
~COL: U45.12 (~CO), U46.5 (UP)
~COR: U20.7 (O7)
~DEC: U80.4 (DOWN)
~DPH: U1.3, U25.5
~Dx: U35.10 (O5), U114.12
~EA: U13.1, U97.1 (1OE), U97.19 (2OE)
~ENTER: U107.12
~EOR: U8.7 (S6), U149.1 (OE), U184.11 (G)
~EXIT: U24.1, U32.6, U50.4 (~S)
~Fx_PRE: U145.10, U217.12
~Fx: U35.15 (O0), U143.13
~GETA: U6.2, U34.13 (O2)
~GETB: U34.15 (O0)
~GETD: U34.12 (O3)
~GETO: U34.14 (O1), U220.5
~GET: U32.3
~IABO: U116.12
~IA_OE: U109.1 (OE), U110.1 (OE), U116.11
~INC: U80.5 (UP)
~IN_RAM: U64.2, U76.20 (~CS)
~IOR: U8.6 (S5), U147.1 (OE), U184.10 (F)
~IRQ: J6.7, U123.1
~LEAVE: U108.12
~LOCAL: U99.1 (1OE), U99.19 (2OE), U136.1 (1OE), U136.19 (2OE)
~MEMOE: U76.22 (~OE), U77.24 (OE), U128.12
~Mx: U35.14 (O1)
~NOP: U20.15 (O0)
~NOT: U8.1 (S0), U184.2 (A), U192.1 (OE)
~Ox: U35.12 (O3), U220.4
~P1BO: U120.1 (OE), U126.1 (OE)
~P2BO: U125.1 (OE), U131.1 (OE)
~P3BO: U117.1 (OE), U119.1 (OE)
~PH0: U5.1 (~Mr), U19.5 (EI), U50.1 (~R), U50.13 (~R), U123.2
~PH3: U144.13, U209.13
~PHA0: U127.1 (~R)
~POE: U41.1 (OE)
~PUTA: U34.9 (O6), U95.12
~PUTB: U24.2, U34.11 (O4)
~PUTD: U34.7 (O7), U114.13
~PUTO: U34.10 (O5)
~PUT: U32.8
~Px: U26.1 (OE), U35.7 (O7)
~RCOPY: U144.10, U174.1
~RES: J6.1, U10.10 (~SRCLR), U17.1 (~Mr), U79.1 (~Mr), U84.1 (~Mr), U88.1 (~Mr), U92.1 (~Mr), U121.1 (~Mr)
~RET: U106.11, U108.13
~RTI: U20.9 (O6), U106.13, U116.13, U132.1 (~R)
~RTS: U20.10 (O5), U106.12
~SCH: U3.4 (~S), U20.11 (O4)
~SCL: U20.12 (O3)
~SCROUNGE: U102.12, U104.12
~SHL: U8.11 (S10), U193.1 (OE)
~SHR: U8.13 (S11), U205.13
~SSI: U20.14 (O1)
~SSO: U20.13 (O2)
~SUBB: U8.17 (S15), U211.13
~SUBR: U21.8, U50.10 (~S)
~SWAP: U8.10 (S9), U87.12
~Sx: U10.13 (~OE), U35.9 (O6)
~TRAP_0: U132.4 (~S)
~TRAP: U25.6, U27.1 (1OE), U27.19 (2OE)
~XA: U6.4, U8.8 (S7), U13.2, U14.5 (S4), U87.13, U184.12 (H)
~hidec: U69.4 (DOWN), U90.6
~hiinc: U69.5 (UP), U103.6
~opc_ALU: U6.1, U8.18 (E0), U22.14 (O1)
~opc_BOP: U22.15 (O0), U47.4 (E1)
~opc_GETPUT: U1.2, U22.12 (O3)
~opc_PAIR: U22.11 (O4), U35.4 (E1), U141.5 (E2), U144.12, U217.11
~opc_SYS: U19.15 (E0), U20.4 (E1)
~opc_TRAP: U22.13 (O2), U25.4
~xB: U14.3 (S2)
~xC: U14.1 (S0), U107.13
~xE: U14.9 (S8)
~xH: U14.15 (S13)
~xJ: U14.14 (S12)
~xK: U14.10 (S9), U130.1 (OE)
~xM_PRE: U146.1, U217.13
~xM: U14.2 (S1)
~xN: U14.17 (S15)
~xO: U14.4 (S3)
~xP: U14.8 (S7)
~xS: U11.1 (~PL), U14.7 (S6)
~xU: U14.11 (S10)
~xW: U14.13 (S11), U127.4 (~S)
~xZ: U14.16 (S14)

Notes on the sheet:
Instruction- Word Latch
(Base) Page Index
GETPUT Decoder
DxD
BOP Decoder
(xU adds 8-bit signed to 16-bit B:O)
Device Enable Register
Adds 1 for 2's complement
Memory @B:O
Start, latch instruction or interrupt vector
Defer latching updated A until CLOSE of instruction, so that old value can be saved in X CLEAR_A: Uses this latch to feed result flags into X, unrelated to content of A!
Secondary Result
Parallel LE
Serial Input Register
LOW ORDER SELECTOR
Low order address byte hardwired address bits in local page ("L1-L8") (OPCODE bits IB... see decoder section left center)
Parallel Output Register
Interrupt Address Pointer
Implements SPI functionality with dedicated SER/DES registers
Hardwire IRQ TRAP instruction: 001.00000 to page 0
Sign
SOR
Sets BUSY flag, disabling interrupts
B:O Pointers
Parallel
Pair SRC Decoder
Put F7h on the bus O will latch
OUT
~8MHz
Any of these disable the updating of X with pushed values or flags from A
Clear Program Counter applied during CLOSE
Serial
Offset
External GPIO BUS
On JUMP: Load target offset on DB into PC
IA used during TRAP/RTI instead of B:O
Except when
Trap calls to page 0 enable "BUSY", disabling Interrupts
Pair DST Decoder
IPH: Instruction Fetch Phase DPH: Data Phase
IN_ROM
Pointer high
ALU Decoder
(PC Program Counter)
Literal Fetch, skip current instruction word Increment PC
SIR
On xU: 8-bit signed on DB added to O, carry/overflow increments decrements B register ("16-bit addition")
O: - Saves offset of current instruction byte during call/trap/cor - Outputs return offset during RET - Is the (only) implied address offset for memory read-write, with the corresponding page index stored in B (Base) - Together with B forms 16-bit address pointers subject to the xU instruction. The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
BO_ = B:O to Pointer
Hot (not zero)
Key ZPAGE offset
8:3 Priority Encoder CD4532
PIR
Copy old value of A into X
Serial IO
Delay ~{SUBR} until CLOSE
BxB
HI7 switches between RAM and ROM
RAM/ROM
D(OWN COUNTER)
-- Opcode Bits -- MSB LSB all 0: OPC_SYS 00000 xxx b0-2: Index of SYS Instruction else: OPC_BOP 00001 xxx b0-2: Index of BOP Instruction OPC_ALU 0001 xxxx b0-3: Index of ALU Instruction OPC_TRAP 001 xxxxx b0-4: DESTPAGE OPC_GETPUT 01 xx x xxx b0-2: OFFS, b3: GET/PUT, b4-5: REG OPC_PAIR 1 xxx xxxx b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
Chip "Footprint" External Connections
Negative
Page index L during GETPUT ops
REGSEL
CARRY, BORROW, MSB shifted out during LSHIFT
(Code Page Index)
Pin40
F7h = 11110111b Corresponds to L0 in local page
RSHIFT
Zero
Byte offset in IB0-2
On RET/COR/xC: Load instruction offset from O into PC, but TRAPs/RTI use IA
OxO
Jump
PxP
NOT
BO Pointer Registers
Base
Jump if A zero
Immediate calls
Carry
Enable
Scrounger
ALU AND
Register at CLOSE to avoid xU adder feedback Registered byte goes to PC module, latched during RET
ADDER
An "Enable Interrupts" instruction replacing RTI would be cleaner, but would have the disadvantage that an IRQ could occur between it and the RTS instruction for leaving the interrupt service handler.
Primary Result
"Output byte onto GPIO bus"
COMP bit if COMP OVF bit if ADDV
On xU: Decrement if no carry and addend negative
LSHIFT
Pin20
ALU EOR
Low order address byte either from ALU reg B, from a hardwired address byte during interpage control flow (call, xI etc) in the local page, or from program counter register (PC) during automatic instruction fetch / Fx literal fetch.
ALU Instructions
Down-Counter
GET/PUT
ALU COMPARATOR
Serial Output Register
While
Inc PC after each instruction cycle or literal fetch
Parallel IO
CLR: Set PC to 0 during SUBR (TRAP/xC). Execution starts at offset zero, "head" of target page
Output B during SUBR but TRAPS/RTI use IA!
Low order address byte Base register
SYS Decoder
On RET: Restore PC value from O register (Center right)
Page index = High order address byte from either L (local stack frame), C (running code page), or B (data pointer) B used during all xMx memory access L used implicitly during GETPUT ops C used during instruction/literal fetch, or interpage control flow
MSB
~{EXIT} (Can exit the current code page): PH3: Register target page-index CLOSE: Load into C
Serial clock out
Disable scrounging for FxC = FC
Pointer low
On EXIT (SUBR/COR) or CODE: Save code page offset into O
REQ
Pin16
Jump if A not zero ("hot")
HIGH ORDER SELECTOR
On xU: 8-bit signed on DB added to O, carry/overflow increments decrements B register ("16-bit addition")
ALU SHIFT
Update Ptr
Instruction Decoder
B active during xM Mx data access instructions.
On xU: Increment high-order if carry and addend positive
On EXIT (SUBR/COR): Save code page index into B for RTSurn
Branching
Flags
Accumulator
BUSY state removed by RTI instruction
Clock Phases
On RESET: Shall reset L, C, PC and BUSY to 0, others can be random.
MxM
2nd register latches at CLOSE (MB is a valid instruction)
LSB shifted out during RSHIFT
Opcode Type Decoder
Pin1
SxS
Call
NOT BUSY
AX (Accumulator)
Myth Microcontroller Reference Schematic
Jump always
The L register is decremented during CALL/TRAP/ENTER and incremented during RET/LEAVE This operations provide single-page local stack frames for nested subroutines. Each local page has "GETPUT" variables called L1-L8 at byte offsets F8h-FFh. The LOCAL instruction sets B:O to L:F7h (L0)
Jump if A negative
OE for ADDV, ALX, AEX and AGX
PHA0: Put page index (C) and byte offset (PC) of instruction on address bus PHA1: Latch opcode or IRQ Trap opcode into IB0-7, pre-decode instruction PHA2: Decode instruction, set up source byte on DB or other action PHA3: Latch results into target registers or other action CLOSE: Finish latching re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
This is correct - the difference is that AX pushes A (into X), XA overwrites A
Arithmetic Carry/ Borrow
Parallel OE
Zero detection
LSB
CODE is handled differently (O can't latch PC via DB)
Fetch
C active during fetch or interpage control flow
Parallel Input Register
AxA
B: - Saves page index of current instruction byte during call/trap/cor - Outputs return page index during RET - Is the (only) implied page index for memory read-write, with the corresponding byte offset stored in O (Offset) - Together with O forms a 16-bit address pointers subject to the xU instruc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
POR
TRAP decoder
ALU Add/Subtract
Two independent 4-bit groups (high/low) feed into 4:16 decoders for device selection
0 NOT Set A to one's complement of A, X unchanged 1 ALX Flag (A<X) in A (255 if true, 0 if false), X unchanged 2 AEX Flag (A==X) in A (255 if true, 0 if false), X unchanged 3 AGX Flag (A>X) in A (255 if true, 0 if false), X unchanged 4 AND Set A to (A AND X), X unchanged 5 IOR Set A to (A OR X), X 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
Input/Output
_BO: Pointer to B:O
Jump while D not zero
Remap ("scrounge") inherent NOPs such as AA, DD etc, and impracticable opcodes such as FM to other instructions
Control Tree
(Local Page Index Register)
Put L on the bus B will latch
Enable scrounging for FxM = KEY
Inner-loops
On instruction fetch: If IRQ and not BUSY, inject "TRAP 0" opcode, else fetch opcode from memory at C:PC
ALU IOR
"Input byte from GPIO bus"
(Page Offset Register)
ADD/SUB
